SeppeBudenaers/Soldeer_Station_Seppe_Budenaers/Media/Pictures/IMG_20230606_203750.jpg

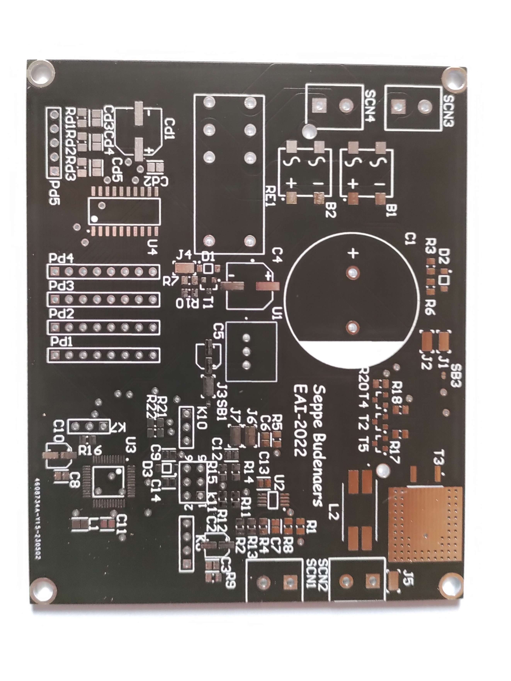
Media/Pictures/IMG_20230606_203750.jpg
